kithousand/Medication-management-aids/AI/hackaton_2_embb/K-000368_0_0_0_0_60_000_200.png

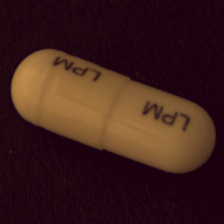
AI/hackaton_2_embb/K-000368_0_0_0_0_60_000_200.png
