kithousand/Medication-management-aids/AI/sample.png

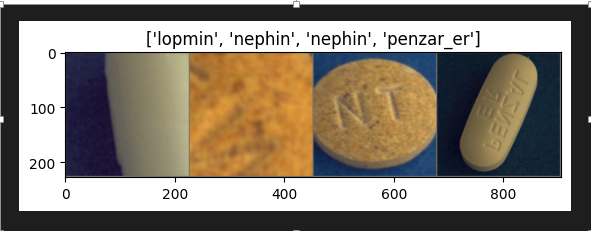
AI/sample.png
