kithousand/Medication-management-aids/Board/picture/그림2.jpg

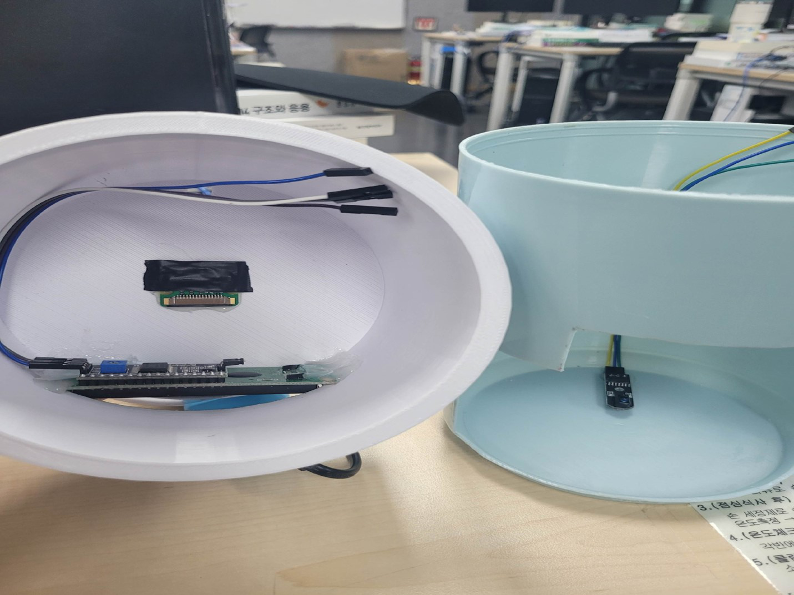
Board/picture/그림2.jpg
