kithousand/Medication-management-aids/Board/picture/그림6.jpg

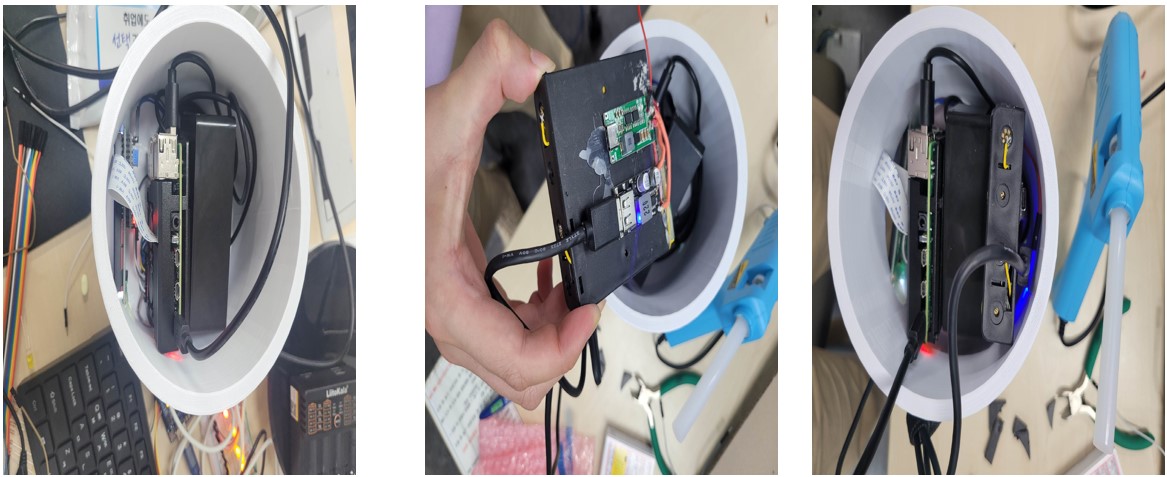
Board/picture/그림6.jpg
