kithousand/Medication-management-aids/Board/picture/그림7.jpg

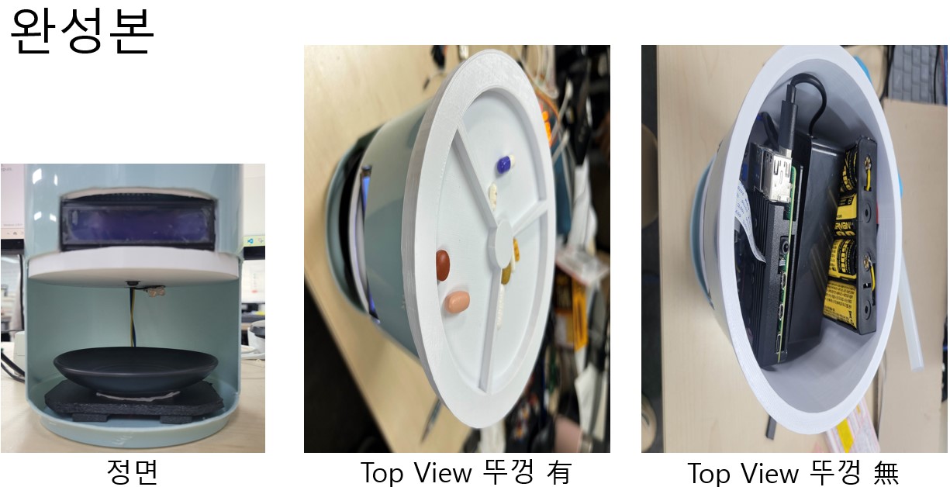
Board/picture/그림7.jpg
