kithousand/Medication-management-aids/Board/배터리팩.png

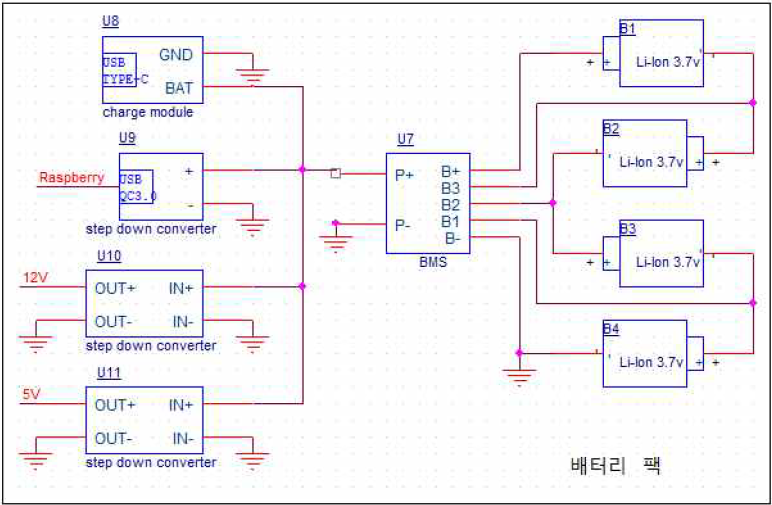
Board/배터리팩.png
