kithousand/Medication-management-aids/Board/회로도.png

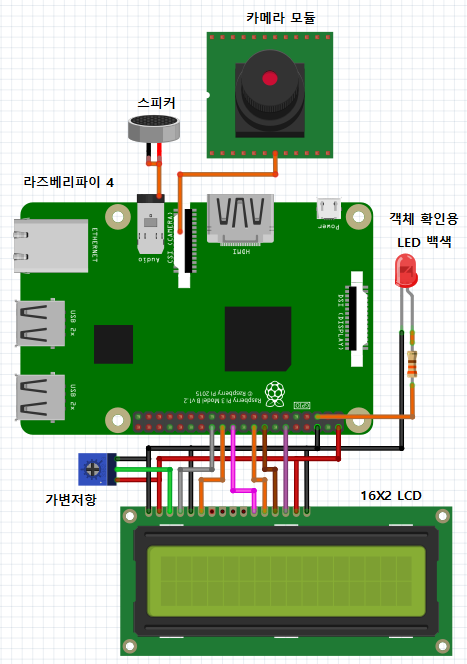
Board/회로도.png
